danielgilbers/maraXshotTimer/bitmaps.h

//Bitmap Data
// 'steam12, 12x12px
const unsigned char PROGMEM steam12[24] = {
  0x10, 0x80, 0x09, 0x00, 0x09, 0x00, 0x10, 0x80, 0x09, 0x00, 0x69, 0x60, 0x81, 0x10, 0x82, 0x10,
  0x60, 0x60, 0x10, 0x80, 0x19, 0x80, 0x06, 0x00
};

// 'steam30', 30x30px
const unsigned char PROGMEM steam30[120] = {
  0x00, 0x00, 0x00, 0x00, 0x00, 0x01, 0x00, 0x00, 0x00, 0x01, 0x00, 0x00, 0x00, 0xc1, 0x06, 0x00,
  0x00, 0xc0, 0x06, 0x00, 0x00, 0x63, 0x0c, 0x00, 0x00, 0xe3, 0x0e, 0x00, 0x01, 0x81, 0x83, 0x00,
  0x01, 0x81, 0x83, 0x00, 0x00, 0xe3, 0x8e, 0x00, 0x00, 0x63, 0x0c, 0x00, 0x00, 0x73, 0x1c, 0x00,
  0x06, 0x31, 0x98, 0xc0, 0x0e, 0x31, 0x98, 0xe0, 0x3c, 0x31, 0x18, 0x70, 0x30, 0xf3, 0x1e, 0x30,
  0x61, 0xe3, 0x0f, 0x18, 0x61, 0x83, 0x03, 0x18, 0xc1, 0x81, 0x03, 0x0c, 0xc0, 0x03, 0x80, 0x0c,
  0x60, 0x02, 0x80, 0x18, 0x60, 0x02, 0x00, 0x18, 0x30, 0x02, 0x00, 0x30, 0x3c, 0x00, 0x00, 0xf0,
  0x0f, 0xc0, 0x0f, 0xc0, 0x07, 0xc0, 0x0f, 0x80, 0x00, 0xe0, 0x1c, 0x00, 0x00, 0x70, 0x38, 0x00,
  0x00, 0x3f, 0xf0, 0x00, 0x00, 0x0f, 0xc0, 0x00
};

// 'coffeeCup12', 12x12px
const unsigned char PROGMEM coffeeCup12[24] = {
  0x02, 0x00, 0x11, 0x00, 0x0a, 0x00, 0x10, 0x00, 0x08, 0x00, 0x7f, 0x80, 0x80, 0x60, 0x80, 0x50,
  0xc0, 0xe0, 0x40, 0x80, 0x61, 0x80, 0x3f, 0x00
};

// 'coffeeCup30', 30x30px
const unsigned char PROGMEM coffeeCups30[9][120] = {
  { 0x00, 0x03, 0x00, 0x00, 0x00, 0x03, 0x00, 0x00, 0x00, 0x06, 0x00, 0x00, 0x00, 0x07, 0x00, 0x00,
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
    0x18, 0x00, 0x03, 0x0c, 0x1c, 0x00, 0x07, 0x1c, 0x0c, 0x04, 0x07, 0xf8, 0x0e, 0x00, 0x0f, 0xf0,
    0x07, 0xff, 0xfc, 0x00, 0x07, 0xff, 0xfc, 0x00, 0x03, 0xff, 0xf8, 0x00, 0x01, 0xff, 0xf0, 0x00,
    0x00, 0xff, 0xe0, 0x00, 0x00, 0x7f, 0xc0, 0x00 },
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
};
